ElfDeMaison/InerCal/FirmWare/include/wifi_config.h

#ifndef WIFI_CONFIG_H
#define WIFI_CONFIG_H

const char* ssid = "ESP32_Access_Point"; // Nom du réseau Wi-Fi que l'ESP32 crée
const char* password = "12345678";  // Mot de passe du réseau (facultatif)

#endif
